felixwittwer/homeassistant_keybowl/pcb/images/keybowl_core_pcb.png

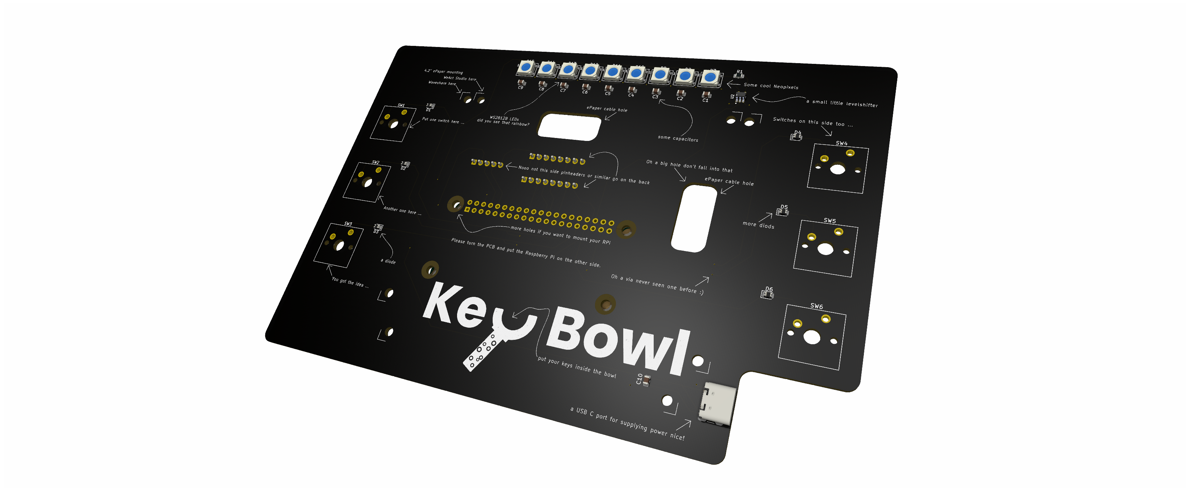
pcb/images/keybowl_core_pcb.png
