felixwittwer/homeassistant_keybowl/production/wooden housing/images/housing_cad.png

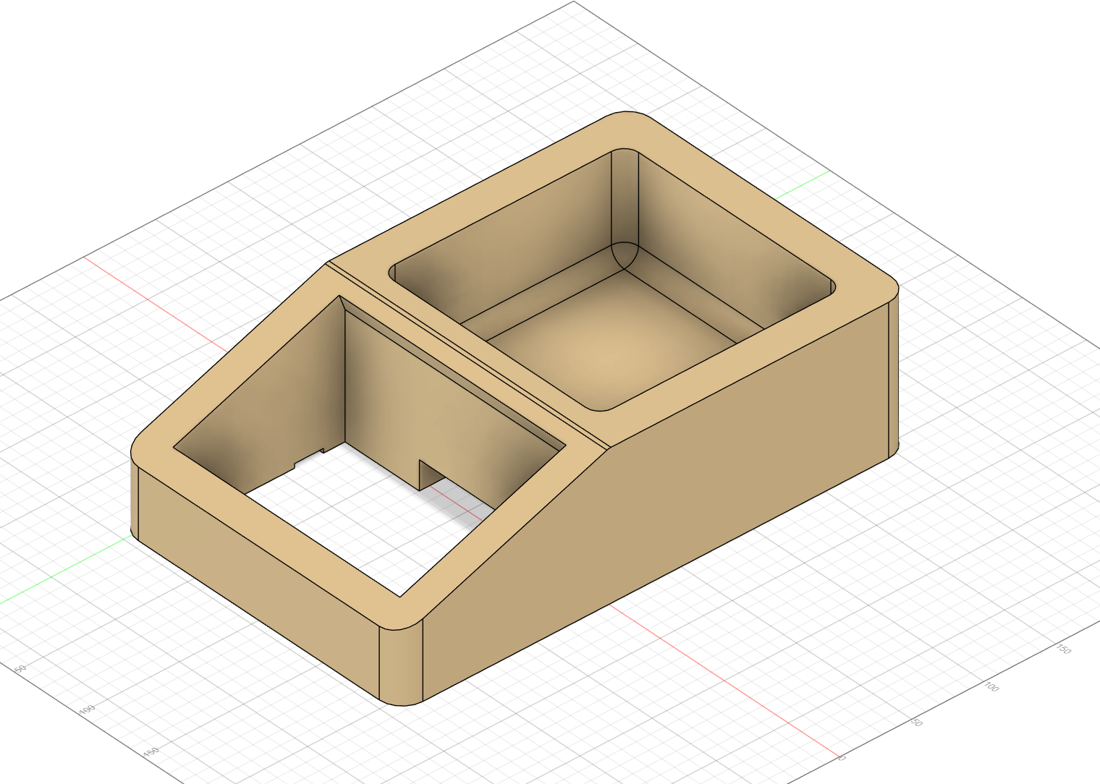
production/wooden housing/images/housing_cad.png
